baptistev7/ESPScale/docs/screens/main_mqtt_ko.png

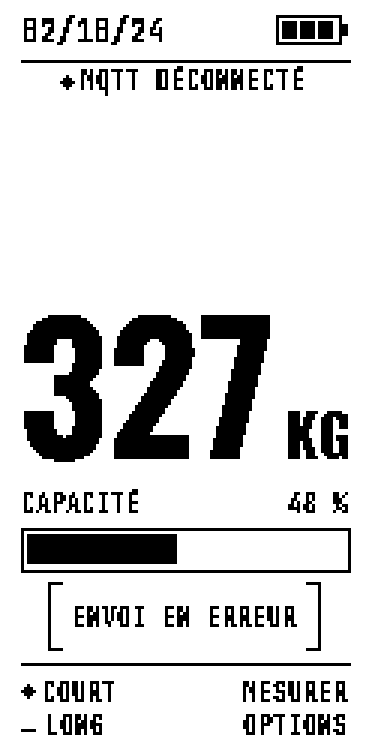
docs/screens/main_mqtt_ko.png
